bendlas/Loko/Software/LokoAir Firmware/loko_air-main/Core/bsp_stm32wle5/stm32wlxx_LoRa_E5_mini_radio.c

/**
 ******************************************************************************
 * @file    stm32wlxx_nucleo_radio.c
 * @author  MCD Application Team
 * @brief   This file provides set of firmware functions to manage:
 *          - RF circuitry available on STM32WLXX-LoRa_E5_mini
 *            Kit from STMicroelectronics
 ******************************************************************************
 * @attention
 *
 * Copyright (c) 2020(-2021) STMicroelectronics.
 * All rights reserved.
 *
 * This software is licensed under terms that can be found in the LICENSE file
 * in the root directory of this software component.
 * If no LICENSE file comes with this software, it is provided AS-IS.
 *
 ******************************************************************************
 */

/* Includes ------------------------------------------------------------------*/
#include "stm32wlxx_LoRa_E5_mini_radio.h"

/** @addtogroup BSP
 * @{
 */

/** @addtogroup STM32WLXX_LoRa_E5_mini
 * @{
 */

/** @addtogroup STM32WLXX_LoRa_E5_mini_RADIO_LOW_LEVEL
 * @brief This file provides set of firmware functions to Radio switch
 *        available on STM32WLXX-Nucleo Kit from STMicroelectronics.
 * @{
 */

/** @addtogroup STM32WLXX_LoRa_E5_mini_RADIO_LOW_LEVEL_Exported_Functions
 * @{
 */

/**
 * @brief  Init Radio Switch
 * @retval BSP status
 */
int32_t bsp_radio_init(void) {
    GPIO_InitTypeDef gpio_init_structure = { 0 };

    /* Enable the Radio Switch Clock */
    RF_SW_CTRL1_GPIO_CLK_ENABLE();

    /* Configure the Radio Switch pin */
    gpio_init_structure.Pin = RF_SW_CTRL1_PIN;
    gpio_init_structure.Mode = GPIO_MODE_OUTPUT_PP;
    gpio_init_structure.Pull = GPIO_NOPULL;
    gpio_init_structure.Speed = GPIO_SPEED_FREQ_VERY_HIGH;

    HAL_GPIO_Init(RF_SW_CTRL1_GPIO_PORT, &gpio_init_structure);

    gpio_init_structure.Pin = RF_SW_CTRL2_PIN;
    HAL_GPIO_Init(RF_SW_CTRL2_GPIO_PORT, &gpio_init_structure);

    HAL_GPIO_WritePin(RF_SW_CTRL2_GPIO_PORT, RF_SW_CTRL2_PIN, GPIO_PIN_RESET);
    HAL_GPIO_WritePin(RF_SW_CTRL1_GPIO_PORT, RF_SW_CTRL1_PIN, GPIO_PIN_RESET);

    return BSP_ERROR_NONE;
}

/**
 * @brief  DeInit Radio Switch
 * @retval BSP status
 */
int32_t bsp_radio_de_init(void) {
    RF_SW_RX_GPIO_CLK_DISABLE();

    /* Turn off switch */
    HAL_GPIO_WritePin(RF_SW_CTRL1_GPIO_PORT, RF_SW_CTRL1_PIN, GPIO_PIN_RESET);
    HAL_GPIO_WritePin(RF_SW_CTRL2_GPIO_PORT, RF_SW_CTRL2_PIN, GPIO_PIN_RESET);

    /* DeInit the Radio Switch pin */
    HAL_GPIO_DeInit(RF_SW_CTRL1_GPIO_PORT, RF_SW_CTRL1_PIN);
    HAL_GPIO_DeInit(RF_SW_CTRL2_GPIO_PORT, RF_SW_CTRL2_PIN);

    return BSP_ERROR_NONE;
}

/**
 * @brief  Configure Radio Switch.
 * @param  Config: Specifies the Radio RF switch path to be set.
 *         This parameter can be one of following parameters:
 *           @arg RADIO_SWITCH_OFF
 *           @arg RADIO_SWITCH_RX
 *           @arg RADIO_SWITCH_RFO_LP
 *           @arg RADIO_SWITCH_RFO_HP
 * @retval BSP status
 */
int32_t bsp_radio_config_rf_switch(BSP_RADIO_Switch_TypeDef config) {
    switch (config) {
        case RADIO_SWITCH_OFF: {
            /* Turn off switch */
            HAL_GPIO_WritePin(RF_SW_CTRL1_GPIO_PORT, RF_SW_CTRL1_PIN, GPIO_PIN_RESET);
            HAL_GPIO_WritePin(RF_SW_CTRL2_GPIO_PORT, RF_SW_CTRL2_PIN, GPIO_PIN_RESET);
            break;
        }

        case RADIO_SWITCH_RX: {
            /*Turns On in Rx Mode the RF Switch */
            HAL_GPIO_WritePin(RF_SW_CTRL1_GPIO_PORT, RF_SW_CTRL1_PIN, GPIO_PIN_SET);
            HAL_GPIO_WritePin(RF_SW_CTRL2_GPIO_PORT, RF_SW_CTRL2_PIN, GPIO_PIN_RESET);
            break;
        }

        case RADIO_SWITCH_RFO_LP: {
            /*Turns On in Tx Low Power the RF Switch */
            HAL_GPIO_WritePin(RF_SW_CTRL1_GPIO_PORT, RF_SW_CTRL1_PIN, GPIO_PIN_SET);
            HAL_GPIO_WritePin(RF_SW_CTRL2_GPIO_PORT, RF_SW_CTRL2_PIN, GPIO_PIN_SET);
            break;
        }

        case RADIO_SWITCH_RFO_HP: {
            /*Turns On in Tx High Power the RF Switch */
            HAL_GPIO_WritePin(RF_SW_CTRL1_GPIO_PORT, RF_SW_CTRL1_PIN, GPIO_PIN_RESET);
            HAL_GPIO_WritePin(RF_SW_CTRL2_GPIO_PORT, RF_SW_CTRL2_PIN, GPIO_PIN_SET);
            break;
        }

        default:
            break;
    }

    return BSP_ERROR_NONE;
}

/**
 * @brief  Return Board Configuration
 * @retval
 *  RADIO_CONF_RFO_LP_HP
 *  RADIO_CONF_RFO_LP
 *  RADIO_CONF_RFO_HP
 */
int32_t bsp_radio_get_tx_config(void) {
    return RADIO_CONF_RFO_HP;
}

/**
 * @brief  Get If TCXO is to be present on board
 * @note   never remove called by MW,
 * @retval
 *  RADIO_CONF_TCXO_NOT_SUPPORTED
 *  RADIO_CONF_TCXO_SUPPORTED
 */
int32_t bsp_radio_is_tcxo(void) {
    return RADIO_CONF_TCXO_SUPPORTED;
}

/**
 * @brief  Get If DCDC is to be present on board
 * @note   never remove called by MW,
 * @retval
 *  RADIO_CONF_DCDC_NOT_SUPPORTED
 *  RADIO_CONF_DCDC_SUPPORTED
 */
int32_t bsp_radio_is_dcdc(void) {
    return RADIO_CONF_DCDC_SUPPORTED;
}

/**
 * @}
 */

/**
 * @}
 */

/**
 * @}
 */

/**
 * @}
 */

/************************ (C) COPYRIGHT STMicroelectronics *****END OF FILE****/
