bendlas/Loko/Software/LokoAir Firmware/loko_air-main/tools/nmea_generator.py

from time import sleep
import serial

nmea = [
b"$GPGGA,211303.299,5441.906,N,02515.825,E,1,12,1.0,0.0,M,0.0,M,,*69\r\n",
b"$GPGSA,A,3,01,02,03,04,05,06,07,08,09,10,11,12,1.0,1.0,1.0*30\r\n",
b"$GPRMC,211303.299,A,5441.906,N,02515.825,E,1116.9,174.3,131222,000.0,W*43\r\n",
b"$GPGGA,211304.299,5441.597,N,02515.856,E,1,12,1.0,0.0,M,0.0,M,,*6E\r\n",
b"$GPGSA,A,3,01,02,03,04,05,06,07,08,09,10,11,12,1.0,1.0,1.0*30\r\n",
b"$GPRMC,211304.299,A,5441.597,N,02515.856,E,1770.7,198.8,131222,000.0,W*45\r\n",
b"$GPGGA,211305.299,5441.115,N,02515.691,E,1,12,1.0,0.0,M,0.0,M,,*64\r\n",
b"$GPGSA,A,3,01,02,03,04,05,06,07,08,09,10,11,12,1.0,1.0,1.0*30\r\n",
b"$GPRMC,211305.299,A,5441.115,N,02515.691,E,1520.3,260.3,131222,000.0,W*43\r\n",
b"$GPGGA,211306.299,5440.996,N,02514.991,E,1,12,1.0,0.0,M,0.0,M,,*6B\r\n",
b"$GPGSA,A,3,01,02,03,04,05,06,07,08,09,10,11,12,1.0,1.0,1.0*30\r\n",
b"$GPRMC,211306.299,A,5440.996,N,02514.991,E,1554.2,212.3,131222,000.0,W*4B\r\n",
b"$GPGGA,211307.299,5440.591,N,02514.733,E,1,12,1.0,0.0,M,0.0,M,,*67\r\n",
b"$GPGSA,A,3,01,02,03,04,05,06,07,08,09,10,11,12,1.0,1.0,1.0*30\r\n",
b"$GPRMC,211307.299,A,5440.591,N,02514.733,E,1851.2,227.3,131222,000.0,W*49\r\n",
b"$GPGGA,211308.299,5440.156,N,02514.259,E,1,12,1.0,0.0,M,0.0,M,,*6E\r\n",
b"$GPGSA,A,3,01,02,03,04,05,06,07,08,09,10,11,12,1.0,1.0,1.0*30\r\n",
b"$GPRMC,211308.299,A,5440.156,N,02514.259,E,2072.3,205.7,131222,000.0,W*4F\r\n",
b"$GPGGA,211309.299,5439.602,N,02513.992,E,1,12,1.0,0.0,M,0.0,M,,*6C\r\n",
b"$GPGSA,A,3,01,02,03,04,05,06,07,08,09,10,11,12,1.0,1.0,1.0*30\r\n",
b"$GPRMC,211309.299,A,5439.602,N,02513.992,E,2612.1,238.1,131222,000.0,W*47\r\n",
b"$GPGGA,211310.299,5439.072,N,02513.137,E,1,12,1.0,0.0,M,0.0,M,,*62\r\n",
b"$GPGSA,A,3,01,02,03,04,05,06,07,08,09,10,11,12,1.0,1.0,1.0*30\r\n",
b"$GPRMC,211310.299,A,5439.072,N,02513.137,E,1868.7,241.8,131222,000.0,W*48\r\n",
b"$GPGGA,211311.299,5438.720,N,02512.477,E,1,12,1.0,0.0,M,0.0,M,,*62\r\n",
b"$GPGSA,A,3,01,02,03,04,05,06,07,08,09,10,11,12,1.0,1.0,1.0*30\r\n",
b"$GPRMC,211311.299,A,5438.720,N,02512.477,E,428.4,245.7,131222,000.0,W*79\r\n",
b"$GPGGA,211312.299,5438.647,N,02512.315,E,1,12,1.0,0.0,M,0.0,M,,*62\r\n",
b"$GPGSA,A,3,01,02,03,04,05,06,07,08,09,10,11,12,1.0,1.0,1.0*30\r\n",
b"$GPRMC,211312.299,A,5438.647,N,02512.315,E,543.4,267.7,131222,000.0,W*75\r\n",
b"$GPGGA,211313.299,5438.637,N,02512.055,E,1,12,1.0,0.0,M,0.0,M,,*63\r\n",
b"$GPGSA,A,3,01,02,03,04,05,06,07,08,09,10,11,12,1.0,1.0,1.0*30\r\n",
b"$GPRMC,211313.299,A,5438.637,N,02512.055,E,333.3,271.9,131222,000.0,W*7B\r\n",
b"$GPGGA,211314.299,5438.642,N,02511.896,E,1,12,1.0,0.0,M,0.0,M,,*62\r\n",
b"$GPGSA,A,3,01,02,03,04,05,06,07,08,09,10,11,12,1.0,1.0,1.0*30\r\n",
b"$GPRMC,211314.299,A,5438.642,N,02511.896,E,194.9,017.1,131222,000.0,W*75\r\n",
b"$GPGGA,211315.299,5438.695,N,02511.912,E,1,12,1.0,0.0,M,0.0,M,,*64\r\n",
b"$GPGSA,A,3,01,02,03,04,05,06,07,08,09,10,11,12,1.0,1.0,1.0*30\r\n",
b"$GPRMC,211315.299,A,5438.695,N,02511.912,E,194.9,017.1,131222,000.0,W*73\r\n"
]

ser = serial.Serial('COM17', 9600, timeout=1)

while True:
    sleep(30)
    for str in nmea:
        print(str)
        ser.write(str)
        sleep(1)
